Makerfabs/MaTouch_ESP32-S3-MaUWB-SPI-TFT-Touch-3.95-ST7796/example/Tag_positioning/3.95_UWB_position/MakerfabsLogo.h

#pragma once

#define MAKERFABS_LOGO_WIDTH 300
#define MAKERFABS_LOGO_HEIGHT 75

const uint16_t makerfabsLogo[MAKERFABS_LOGO_WIDTH * MAKERFABS_LOGO_HEIGHT] PROGMEM = {
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
};
