Makerfabs/MaTouch_ESP32-S3-MaUWB-SPI-TFT-Touch-3.95-ST7796/example/Tag_positioning/3.95_UWB_position/FT6236.h

#include <Wire.h>

#define TOUCH_I2C_ADD 0x38

#define TOUCH_REG_TD_STATUS 0x02
#define TOUCH_REG_XL 0x04
#define TOUCH_REG_XH 0x03
#define TOUCH_REG_YL 0x06
#define TOUCH_REG_YH 0x05

int readTouchReg(int reg);

int getTouchPointX();

int getTouchPointY();

int ft6236_pos(int pos[2]);
